pronvis/drawer-robot/documentation/dymh-106/connection_2.png

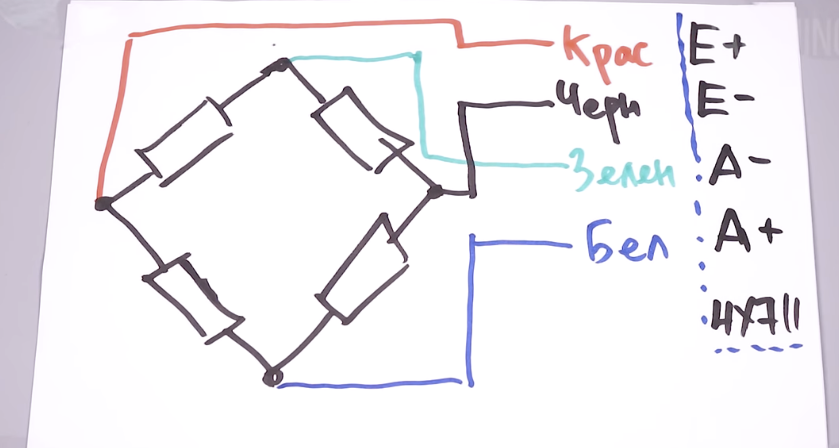
documentation/dymh-106/connection_2.png
