pronvis/drawer-robot/documentation/dymh-106/connection_to_translate.png

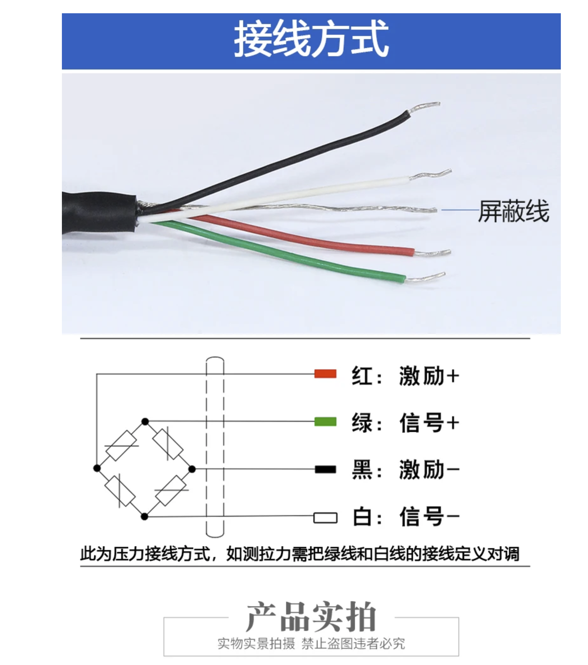
documentation/dymh-106/connection_to_translate.png
