pronvis/drawer-robot/documentation/hc-05/hc05_error_codes.jpg

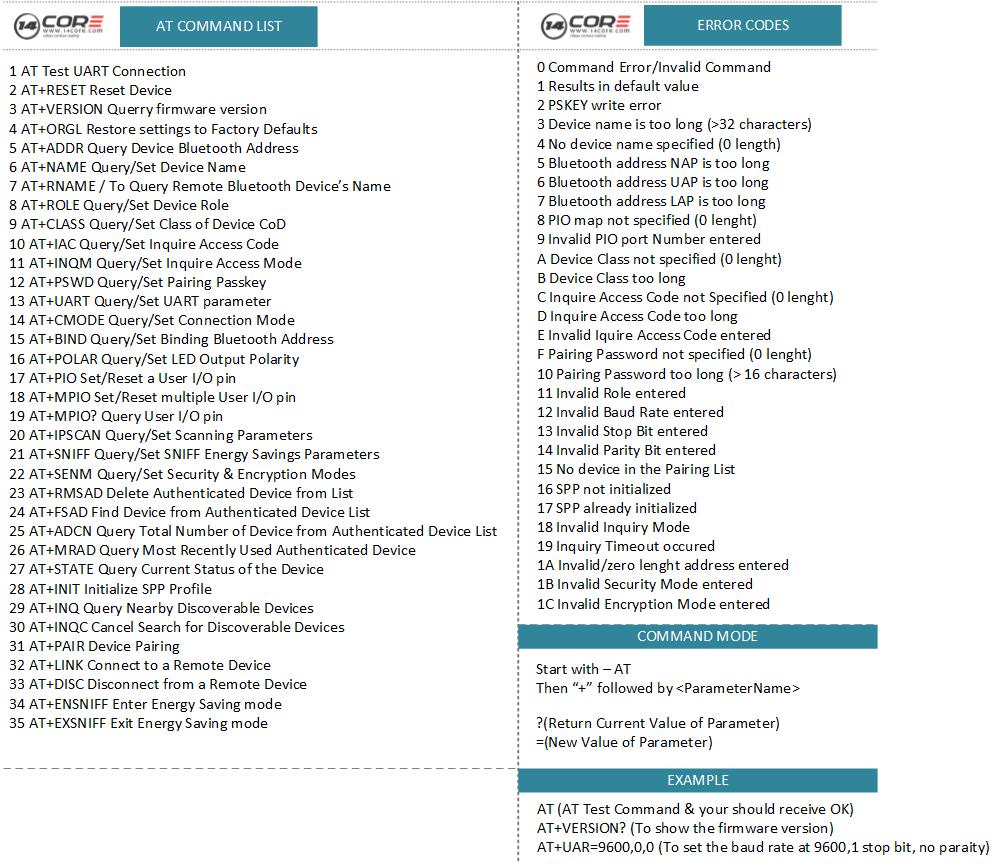
documentation/hc-05/hc05_error_codes.jpg
