pronvis/drawer-robot/hc05_arduino_configurator/HC05_connection_diagram.jpg

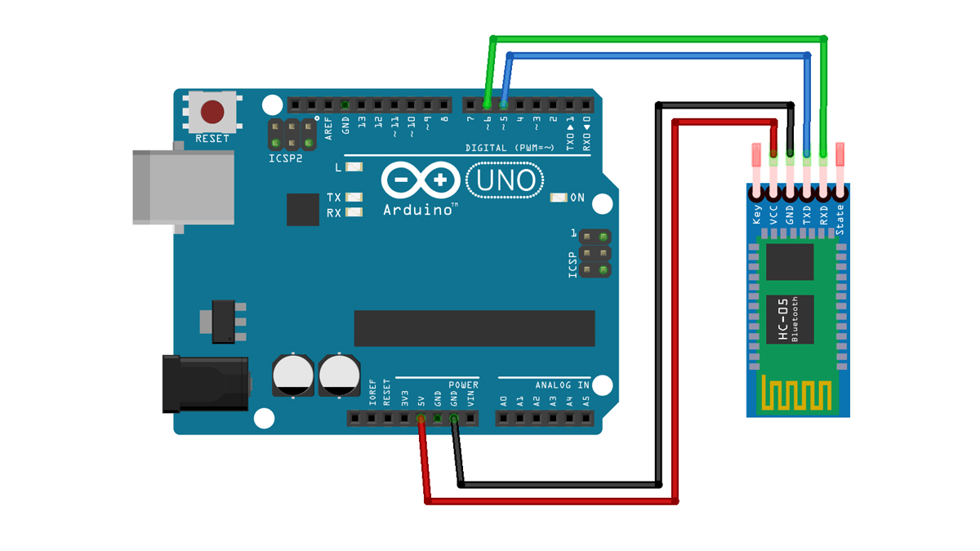
hc05_arduino_configurator/HC05_connection_diagram.jpg
