pronvis/drawer-robot/src/bin/steps_with_potentiometr.rs

#![no_main]
#![no_std]
#![feature(type_alias_impl_trait)]

use drawer_robot as _; // global logger + panicking-behavior + memory layout

#[rtic::app(
    device = stm32f1xx_hal::pac,
    peripherals = true,
    // You can usually find the names of the interrupt vectors in the some_hal::pac::interrupt enum.
    dispatchers = [EXTI0, EXTI1, EXTI2, EXTI3, EXTI4]
    // dispatchers = [PVD, WWDG, RTC, SPI1]
)]
mod app {
    use fugit::ExtU32;

    use drawer_robot::*;
    use rtic_monotonics::systick::*;
    use rtic_sync::{channel::*, make_channel};
    use stm32f1xx_hal::{
        adc::{self, Adc},
        device::ADC1,
        pac,
        prelude::*,
    };

    //COPYPASTE (same in src/bin/steps_by_timer_with_potentiometr.rs)
    pub async fn read_potent(adc1: &mut Adc<ADC1>, pb0: &mut stm32f1xx_hal::gpio::Pin<'B', 0, stm32f1xx_hal::gpio::Analog>) -> u16 {
        //sum 10 measurments - max value 4.1k, so 41k which can be still stored in u16
        let mut sum: u16 = 0;
        for _ in 0..10 {
            let data: u16 = adc1.read(pb0).unwrap();
            sum += data;
            Systick::delay(10.millis()).await;
        }

        return sum / 10;
    }

    pub fn calc_steps_delay(potent_value: u16) -> u32 {
        let min_delay: u32 = 700_000;
        let potent_shift: u32 = u32::from(potent_value) / 100 * 30_0000;
        return min_delay + potent_shift;
    }
    /////////////////////////////////////////////////////////////////

    const STEPPER_CLOCK_FREQ: u32 = 72_000_000;
    const CHANNEL_CAPACITY: usize = 1;

    #[shared]
    struct Shared {}

    #[local]
    struct Local {
        step_pin: StepPin,
        adc1: Adc<ADC1>,
        pb0: stm32f1xx_hal::gpio::Pin<'B', 0, stm32f1xx_hal::gpio::Analog>,
    }

    #[init]
    fn init(mut cx: init::Context) -> (Shared, Local) {
        defmt::info!("init");

        // Take ownership over the raw flash and rcc devices and convert them into the corresponding
        // HAL structs
        let mut flash: stm32f1xx_hal::flash::Parts = cx.device.FLASH.constrain();
        let mut rcc: stm32f1xx_hal::rcc::Rcc = cx.device.RCC.constrain();

        // Freeze the configuration of all the clocks in the system and store the frozen frequencies in
        // `clocks`
        // with those values one second equals 'delay_cycles: u32 = 72_000_000'
        let clocks = rcc
            .cfgr
            .use_hse(8.MHz())
            .sysclk(72.MHz())
            .pclk1(36.MHz())
            .pclk2(72.MHz())
            .freeze(&mut flash.acr);

        if !clocks.usbclk_valid() {
            panic!("Clock parameter values are wrong!");
        }

        // Acquire the GPIOC peripheral
        let mut gpioc: stm32f1xx_hal::gpio::gpioc::Parts = cx.device.GPIOC.split();

        ////////////////////////////
        ////////////////////////////
        // Motor Driver Configuration

        let mut gpiob: stm32f1xx_hal::gpio::gpiob::Parts = cx.device.GPIOB.split();

        let mut en = gpioc.pc15.into_push_pull_output(&mut gpioc.crh);
        en.set_low();
        let step = gpioc.pc6.into_push_pull_output(&mut gpioc.crl);
        let mut dir = gpioc.pc13.into_push_pull_output(&mut gpioc.crh);
        dir.set_low();

        let mut adc1 = adc::Adc::adc1(cx.device.ADC1, clocks);
        // Configure pb0 as an analog input
        let mut pb0 = gpiob.pb0.into_analog(&mut gpiob.crl);

        let systick_mono_token = rtic_monotonics::create_systick_token!();
        Systick::start(cx.core.SYST, STEPPER_CLOCK_FREQ, systick_mono_token);

        let (sender, receiver) = make_channel!(u32, CHANNEL_CAPACITY);
        task::spawn(receiver).ok();
        task1::spawn(sender).ok();

        (Shared {}, Local { step_pin: step, adc1, pb0 })
    }

    // Optional idle, can be removed if not needed.
    #[idle]
    fn idle(_: idle::Context) -> ! {
        defmt::debug!("idle");

        loop {
            cortex_m::asm::nop();
        }
    }

    #[task(priority = 2, local = [ step_pin, current_delay: u32 = 1_000_000])]
    async fn task(cx: task::Context, mut receiver: Receiver<'static, u32, CHANNEL_CAPACITY>) {
        defmt::debug!("Move motor!");

        loop {
            cx.local.step_pin.set_high();
            Systick::delay(2000.nanos()).await;
            cx.local.step_pin.set_low();
            Systick::delay(2000.nanos()).await;

            if !receiver.is_empty() {
                let new_delay = receiver.try_recv().unwrap();
                if new_delay != *cx.local.current_delay {
                    *cx.local.current_delay = new_delay;
                    defmt::debug!("new delay: {}", new_delay);
                }
            }
            Systick::delay(cx.local.current_delay.nanos()).await;
        }
    }

    #[task(priority = 1, local = [adc1, pb0])]
    async fn task1(cx: task1::Context, mut sender: Sender<'static, u32, CHANNEL_CAPACITY>) {
        // potentiometr min value: 0; max: 4100

        loop {
            let potent_value = read_potent(cx.local.adc1, cx.local.pb0).await;
            let new_steps_delay = calc_steps_delay(potent_value);
            if sender.is_empty() {
                sender.send(new_steps_delay).await.unwrap();
            }

            Systick::delay(500.millis()).await;
        }
    }
}
