pronvis/drawer-robot/crates/robot-core/src/robot/mod.rs

mod arm;

use crate::{
    ps3::{Ps3Command, Ps3DigitalCommand},
    DisplayMemoryPool, {display, DisplayString},
};
use arm::RobotArms;
use core::fmt::Write;
use heapless::pool::singleton::Box;
use rtic_sync::channel::{ReceiveError, Receiver, Sender};

pub const HC05_CALIBRATE_ADS1256_CODE: u8 = 221;
pub const TENSION_DATA_CHANNEL_CAPACITY: usize = 32;

const DISPLAY_CHANNEL_CAPACITY: usize = crate::display::CHANNEL_CAPACITY;
const PS3_CHANNEL_CAPACITY: usize = crate::ps3::CHANNEL_CAPACITY;
const COMMUNICATOR_CHANNEL_CAPACITY: usize = crate::my_tmc2209::communicator::CHANNEL_CAPACITY;

pub type Tmc2209Request = crate::my_tmc2209::Request;
pub type Ps3CommandsReceiver = Receiver<'static, Ps3Command, PS3_CHANNEL_CAPACITY>;
pub type TensionDataReceiver = Receiver<'static, TensionData, TENSION_DATA_CHANNEL_CAPACITY>;
pub type Tmc2209CommandsSender = Sender<'static, Tmc2209Request, COMMUNICATOR_CHANNEL_CAPACITY>;

#[derive(Debug, Copy, Clone)]
pub struct TensionData {
    pub t0: i32,
    pub t1: i32,
    pub t2: i32,
    pub t3: i32,
}

pub enum RobotCommand {
    CalibrateAds1256,
    SetFreeTension,
    SetByTension,

    PreviousMotor,
    NextMotor,
    SpeedUp,
    SpeedDown,
    StopMotor,
}

impl From<Ps3Command> for Option<RobotCommand> {
    fn from(value: Ps3Command) -> Self {
        match value {
            Ps3Command::Digital(command) => match command {
                Ps3DigitalCommand::TRIANGLE_DOWN => Some(RobotCommand::CalibrateAds1256),
                Ps3DigitalCommand::CIRCLE_DOWN => Some(RobotCommand::SetByTension),
                Ps3DigitalCommand::SQUARE_DOWN => Some(RobotCommand::SetFreeTension),
                Ps3DigitalCommand::LEFT_DOWN => Some(RobotCommand::PreviousMotor),
                Ps3DigitalCommand::RIGHT_DOWN => Some(RobotCommand::NextMotor),
                Ps3DigitalCommand::UP_DOWN => Some(RobotCommand::SpeedUp),
                Ps3DigitalCommand::DOWN_DOWN => Some(RobotCommand::SpeedDown),
                Ps3DigitalCommand::L1_DOWN => Some(RobotCommand::StopMotor),
                _ => None,
            },
            Ps3Command::Stick(_) => None,
            Ps3Command::OnConnect => None,
        }
    }
}

pub struct Robot {
    stepper_0: Tmc2209CommandsSender,
    stepper_1: Tmc2209CommandsSender,
    stepper_2: Tmc2209CommandsSender,
    stepper_3: Tmc2209CommandsSender,
    ps3_commands_receiver: Ps3CommandsReceiver,
    tension_data_receiver: TensionDataReceiver,
    hc05_tx: stm32f1xx_hal::serial::Tx1,
    display_sender: Sender<'static, Box<DisplayMemoryPool>, DISPLAY_CHANNEL_CAPACITY>,
    arms: RobotArms,
    arm_index: u8,
}

impl Robot {
    pub fn new(
        stepper_0: Tmc2209CommandsSender,
        stepper_1: Tmc2209CommandsSender,
        stepper_2: Tmc2209CommandsSender,
        stepper_3: Tmc2209CommandsSender,
        ps3_commands_receiver: Ps3CommandsReceiver,
        tension_data_receiver: TensionDataReceiver,
        hc05_tx: stm32f1xx_hal::serial::Tx1,
        display_sender: Sender<'static, Box<DisplayMemoryPool>, DISPLAY_CHANNEL_CAPACITY>,
    ) -> Self {
        Robot {
            stepper_0,
            stepper_1,
            stepper_2,
            ps3_commands_receiver,
            stepper_3,
            tension_data_receiver,
            hc05_tx,
            display_sender,
            arms: Default::default(),
            arm_index: 0,
        }
    }

    pub async fn work(&mut self) {
        self.ps3_handler();
        self.tension_handler();

        let arms_speed = self.arms.get_speed();
        let arm0_speed = arms_speed.s0;
        if let Some(arm0_speed) = arm0_speed {
            let write_req = tmc2209::write_request(0, tmc2209::reg::VACTUAL(arm0_speed));
            let req = crate::my_tmc2209::Request::write(write_req);
            self.stepper_0.send(req).await.ok();
        }
        let arm1_speed = arms_speed.s1;
        if let Some(arm1_speed) = arm1_speed {
            let write_req = tmc2209::write_request(0, tmc2209::reg::VACTUAL(arm1_speed));
            let req = crate::my_tmc2209::Request::write(write_req);
            self.stepper_1.send(req).await.ok();
        }
        let arm2_speed = arms_speed.s2;
        if let Some(arm2_speed) = arm2_speed {
            let write_req = tmc2209::write_request(0, tmc2209::reg::VACTUAL(arm2_speed));
            let req = crate::my_tmc2209::Request::write(write_req);
            self.stepper_2.send(req).await.ok();
        }
        let arm3_speed = arms_speed.s3;
        if let Some(arm3_speed) = arm3_speed {
            let write_req = tmc2209::write_request(0, tmc2209::reg::VACTUAL(arm3_speed));
            let req = crate::my_tmc2209::Request::write(write_req);
            self.stepper_3.send(req).await.ok();
        }
    }

    fn ps3_handler(&mut self) {
        match self.ps3_commands_receiver.try_recv() {
            Ok(event) => {
                let command: Option<RobotCommand> = event.into();
                if let Some(c) = command {
                    self.receive_command(c);
                }
            }
            Err(err) => {
                if err == ReceiveError::NoSender {
                    defmt::error!("fail to receive command from channel: ReceiveError::NoSender");
                    return;
                }
            }
        }
    }

    fn tension_handler(&mut self) {
        let mut tension_data: Option<TensionData> = None;
        //read all messages from channel
        while let Ok(data) = self.tension_data_receiver.try_recv() {
            tension_data = Some(data);
        }

        if let Some(tension_data) = tension_data {
            self.arms.set_tension(tension_data);
        }
    }

    #[rustfmt::skip]
    fn receive_command(&mut self, event: RobotCommand) {
        match event {
            RobotCommand::SetFreeTension => {
                self.arms.set_free_tenstion_mode();

                let mut data_str = DisplayString::new();
                write!(data_str, "Arms in Free Mode").expect("not written");
                display::display_str_sync(data_str, &mut self.display_sender).ok();
            },
            RobotCommand::SetByTension => {
                self.arms.set_by_tenstion_mode();

                let mut data_str = DisplayString::new();
                write!(data_str, "Arms in By Tension Mode").expect("not written");
                display::display_str_sync(data_str, &mut self.display_sender).ok();
            },
            RobotCommand::CalibrateAds1256 => {
                if let Err(err) = self.hc05_tx.write(HC05_CALIBRATE_ADS1256_CODE) {
                    defmt::error!("Fail to send 'Calibrate' message to hc05: {:?}", defmt::Debug2Format(&err))
                } else {
                    defmt::debug!("Successfully send message via hc05");
                }
            },

            RobotCommand::PreviousMotor => {
                if self.arm_index == 0  {
                    self.arm_index = 3;
                } else {
                    self.arm_index = self.arm_index - 1;
                }
                
                let mut data_str = DisplayString::new();
                let arm_speed  = self.arms.get_arm(self.arm_index).map_or(0, |arm| arm.get_speed(self.arm_index).unwrap_or(0));
                write!(data_str, "Arm {0} speed: {1}", self.arm_index, arm_speed).expect("not written");
                display::display_str_sync(data_str, &mut self.display_sender).ok();
            },
            RobotCommand::NextMotor => {
                self.arm_index = (self.arm_index + 1) % 4;
                let mut data_str = DisplayString::new();
                let arm_speed  = self.arms.get_arm(self.arm_index).map_or(0, |arm| arm.get_speed(self.arm_index).unwrap_or(0));
                write!(data_str, "Arm {0} speed: {1}", self.arm_index, arm_speed).expect("not written");
                display::display_str_sync(data_str, &mut self.display_sender).ok();
            },

            RobotCommand::SpeedUp => {
                self.arms.get_arm(self.arm_index).map(|arm| arm.increase_speed(15_000));
            },
            RobotCommand::SpeedDown => {
                self.arms.get_arm(self.arm_index).map(|arm| arm.decrease_speed(15_000));
            },
            RobotCommand::StopMotor => {
                self.arms.get_arm(self.arm_index).map(|arm| arm.stop());
            },
        }
    }
}
